circuitvalley/mipi_csi_receiver_FPGA/Cypress FX3 USB3.0 Firmware/cyfxuvcdscr.c

/*
 ## Cypress FX3 Camera Kit Source file (cyfxuvcdscr.c)
 ## ===========================
 ##
 ##  Copyright Cypress Semiconductor Corporation, 2010-2012,
 ##  All Rights Reserved
 ##  UNPUBLISHED, LICENSED SOFTWARE.
 ##
 ##  CONFIDENTIAL AND PROPRIETARY INFORMATION
 ##  WHICH IS THE PROPERTY OF CYPRESS.
 ##
 ##  Use of this file is governed
 ##  by the license agreement included in the file
 ##
 ##     <install>/license/license.txt
 ##
 ##  where <install> is the Cypress software
 ##  installation root directory path.
 ##
 ## ===========================
*/

/*
 * This file contains the USB descriptors for the FX3 HD 720p camera kit
 * application.
 */

#include "uvc.h"
#include "camera_ptzcontrol.h"
#include "uvc_settings.h"


/* Standard Device Descriptor */
const uint8_t CyFxUSBDeviceDscr[] =
    {
        0x12,                           /* Descriptor Size */
        CY_U3P_USB_DEVICE_DESCR,        /* Device Descriptor Type */
        0x10,0x02,                      /* USB 2.0 */
        0xEF,                           /* Device Class */
        0x02,                           /* Device Sub-class */
        0x01,                           /* Device protocol */
        0x40,                           /* Maxpacket size for EP0 : 64 bytes */
        0xB4,0x04,                      /* Vendor ID */
        0xF8,0x00,                      /* Product ID */
        0x00,0x00,                      /* Device release number */
        0x01,                           /* Manufacture string index */
        0x02,                           /* Product string index */
        0x00,                           /* Serial number string index */
        0x01                            /* Number of configurations */
    };

/* Device Descriptor for SS */
const uint8_t CyFxUSBDeviceDscrSS[] =
    {
        0x12,                           /* Descriptor Size */
        CY_U3P_USB_DEVICE_DESCR,        /* Device Descriptor Type */
        0x10,0x03,                      /* USB 3.10 */
        0xEF,                           /* Device Class */
        0x02,                           /* Device Sub-class */
        0x01,                           /* Device protocol */
        0x09,                           /* Maxpacket size for EP0 : 2^9 Bytes */
        0xB4,0x04,                      /* Vendor ID */
        0xF9,0x00,                      /* Product ID */
        0x00,0x00,                      /* Device release number */
        0x01,                           /* Manufacture string index */
        0x02,                           /* Product string index */
        0x00,                           /* Serial number string index */
        0x01                            /* Number of configurations */
    };

/* Standard Device Qualifier Descriptor */
const uint8_t CyFxUSBDeviceQualDscr[] =
    {
        0x0A,                           /* Descriptor Size */
        CY_U3P_USB_DEVQUAL_DESCR,       /* Device Qualifier Descriptor Type */
        0x00,0x02,                      /* USB 2.0 */
        0xEF,                           /* Device Class */
        0x02,                           /* Device Sub-class */
        0x01,                           /* Device protocol */
        0x40,                           /* Maxpacket size for EP0 : 64 bytes */
        0x01,                           /* Number of configurations */
        0x00                            /* Reserved */
    };

/* Standard Full Speed Configuration Descriptor */
const uint8_t CyFxUSBFSConfigDscr[] =
    {
        /* Configuration Descriptor Type */
        0x09,                           /* Descriptor Size */
        CY_U3P_USB_CONFIG_DESCR,        /* Configuration Descriptor Type */
        0x95,0x00,                      /* Length of this descriptor and all sub descriptors */
        0x02,                           /* Number of interfaces */
        0x01,                           /* Configuration number */
        0x00,                           /* COnfiguration string index */
        0x80,                           /* Config characteristics - Bus powered */
        0x32,                           /* Max power consumption of device (in 2mA unit) : 100mA */

        /* Interface Association Descriptor */
        0x08,                           /* Descriptor Size */
        CY_FX_INTF_ASSN_DSCR_TYPE,      /* Interface Association Descr Type: 11 */
        0x00,                           /* I/f number of first VideoControl i/f */
        0x02,                           /* Number of Video i/f */
        0x0E,                           /* CC_VIDEO : Video i/f class code */
        0x03,                           /* SC_VIDEO_INTERFACE_COLLECTION : Subclass code */
        0x00,                           /* Protocol : Not used */
        0x02,                           /* String desc index for interface */

        /* Standard Video Control Interface Descriptor */
        0x09,                           /* Descriptor size */
        CY_U3P_USB_INTRFC_DESCR,        /* Interface Descriptor type */
        0x00,                           /* Interface number */
        0x00,                           /* Alternate setting number */
        0x01,                           /* Number of end points */
        0x0E,                           /* CC_VIDEO : Interface class */
        0x01,                           /* CC_VIDEOCONTROL : Interface sub class */
        0x00,                           /* Interface protocol code */
        0x02,                           /* Interface descriptor string index */

        /* Class specific VC Interface Header Descriptor */
        0x0D,                           /* Descriptor size */
        0x24,                           /* Class Specific I/f Header Descriptor type */
        0x01,                           /* Descriptor Sub type : VC_HEADER */
        0x10, 0x01,                     /* Revision of UVC class spec: 1.1 - Minimum version required
                                           for USB Compliance. Not supported on Windows XP*/
        0x51, 0x00,                     /* Total Size of class specific descriptors (till Output terminal) */
        0x00,0x6C,0xDC,0x02,            /* Clock frequency : 48MHz(Deprecated) */
        0x01,                           /* Number of streaming interfaces */
        0x01,                           /* Video streaming I/f 1 belongs to VC i/f */

        /* Input (Camera) Terminal Descriptor */
        0x12,                           /* Descriptor size */
        0x24,                           /* Class specific interface desc type */
        0x02,                           /* Input Terminal Descriptor type */
        0x01,                           /* ID of this terminal */
        0x01,0x02,                      /* Camera terminal type */
        0x00,                           /* No association terminal */
        0x00,                           /* String desc index : Not used */
#ifdef UVC_PTZ_SUPPORT
        (uint8_t)(wObjectiveFocalLengthMin&0xFF),
        (uint8_t)((wObjectiveFocalLengthMin>>8)&0xFF),
        (uint8_t)(wObjectiveFocalLengthMax&0xFF),
        (uint8_t)((wObjectiveFocalLengthMax>>8)&0xFF),
        (uint8_t)(wOcularFocalLength&0xFF),
        (uint8_t)((wOcularFocalLength>>8)&0xFF),
#else
        0x00,0x00,                      /* No optical zoom supported */
        0x00,0x00,                      /* No optical zoom supported */
        0x00,0x00,                      /* No optical zoom supported */
#endif
        0x03,                           /* Size of controls field for this terminal : 3 bytes */
        0x00,0x00,0x00,                 /* bmControls field of camera terminal: No controls supported */

        /* Processing Unit Descriptor */
        0x0D,                           /* Descriptor size */
        0x24,                           /* Class specific interface desc type */
        0x05,                           /* Processing Unit Descriptor type */
        0x02,                           /* ID of this terminal */
        0x01,                           /* Source ID : 1 : Conencted to input terminal */
        0x00,0x40,                      /* Digital multiplier */
        0x03,                           /* Size of controls field for this terminal : 3 bytes */
        0x00,0x00,0x00,                 /* bmControls field of processing unit: Brightness control supported */
        0x00,                           /* String desc index : Not used */
        0x00,                           /* Analog Video Standards Supported: None */

        /* Extension Unit Descriptor */
        0x1C,                           /* Descriptor size */
        0x24,                           /* Class specific interface desc type */
        0x06,                           /* Extension Unit Descriptor type */
        0x03,                           /* ID of this terminal */
        0xFF,0xFF,0xFF,0xFF,            /* 16 byte GUID */
        0xFF,0xFF,0xFF,0xFF,
        0xFF,0xFF,0xFF,0xFF,
        0xFF,0xFF,0xFF,0xFF,
        0x00,                           /* Number of controls in this terminal */
        0x01,                           /* Number of input pins in this terminal */
        0x02,                           /* Source ID : 2 : Connected to Proc Unit */
        0x03,                           /* Size of controls field for this terminal : 3 bytes */
        0x00,0x00,0x00,                 /* No controls supported */
        0x00,                           /* String desc index : Not used */

        /* Output Terminal Descriptor */
        0x09,                           /* Descriptor size */
        0x24,                           /* Class specific interface desc type */
        0x03,                           /* Output Terminal Descriptor type */
        0x04,                           /* ID of this terminal */
        0x01,0x01,                      /* USB Streaming terminal type */
        0x00,                           /* No association terminal */
        0x03,                           /* Source ID : 3 : Connected to Extn Unit */
        0x00,                           /* String desc index : Not used */

        /* Video Control Status Interrupt Endpoint Descriptor */
        0x07,                           /* Descriptor size */
        CY_U3P_USB_ENDPNT_DESCR,        /* Endpoint Descriptor Type */
        CY_FX_EP_CONTROL_STATUS,        /* Endpoint address and description */
        CY_U3P_USB_EP_INTR,             /* Interrupt End point Type */
        0x40,0x00,                      /* Max packet size = 64 bytes */
        0x08,                           /* Servicing interval : 8ms */

        /* Class Specific Interrupt Endpoint Descriptor */
        0x05,                           /* Descriptor size */
        0x25,                           /* Class Specific Endpoint Descriptor Type */
        CY_U3P_USB_EP_INTR,             /* End point Sub Type */
        0x40,0x00,                      /* Max packet size = 64 bytes */

        /* Standard Video Streaming Interface Descriptor (Alternate Setting 0) */
        0x09,                           /* Descriptor size */
        CY_U3P_USB_INTRFC_DESCR,        /* Interface Descriptor type */
        0x01,                           /* Interface number */
        0x00,                           /* Alternate setting number */
        0x01,                           /* Number of end points : Zero Bandwidth */
        0x0E,                           /* Interface class : CC_VIDEO */
        0x02,                           /* Interface sub class : CC_VIDEOSTREAMING */
        0x00,                           /* Interface protocol code : Undefined */
        0x00,                           /* Interface descriptor string index */

       /* Class-specific Video Streaming Input Header Descriptor */
        0x0E,                           /* Descriptor size */
        0x24,                           /* Class-specific VS I/f Type */
        0x01,                           /* Descriptotor Subtype : Input Header */
        0x00,                           /* No format desciptor supported for FS device */
        0x0E,0x00,                      /* Total size of Class specific VS descr */
        CY_FX_EP_BULK_VIDEO,            /* EP address for BULK video data */
        0x00,                           /* No dynamic format change supported */
        0x04,                           /* Output terminal ID : 4 */
        0x01,                           /* Still image capture method 1 supported */
        0x00,                           /* Hardware trigger NOT supported */
        0x00,                           /* Hardware to initiate still image capture NOT supported */
        0x01,                           /* Size of controls field : 1 byte */
        0x00,                           /* D2 : Compression quality supported */

        /* Endpoint Descriptor for BULK Streaming Video Data */
        0x07,                           /* Descriptor size */
        CY_U3P_USB_ENDPNT_DESCR,        /* Endpoint Descriptor Type */
        CY_FX_EP_BULK_VIDEO,            /* Endpoint address and description */
        0x02,                           /* BULK End point */
        0x40,                           /* EP Packet Size: 64 bytes */
        0x00,
        0x00                            /* Servicing interval for data transfers */
    };

/* Standard High Speed Configuration Descriptor */
const uint8_t CyFxUSBHSConfigDscr[] =
    {
        /* Configuration Descriptor Type */
        0x09,                           /* Descriptor Size */
        CY_U3P_USB_CONFIG_DESCR,        /* Configuration Descriptor Type */
#ifdef USB_DEBUG_INTERFACE
#ifdef FX3_UVC_1_0_SUPPORT
        0xE4,0x00,                      /* Length of this descriptor and all sub descriptors */
#else
        0xE5,0x00,                      /* Length of this descriptor and all sub descriptors */
#endif
        0x03,                           /* Number of interfaces */
#else
#ifdef FX3_UVC_1_0_SUPPORT
        0xCD,0x00,                      /* Length of this descriptor and all sub descriptors */
#else
        0xCE,0x00,                      /* Length of this descriptor and all sub descriptors */
#endif
        0x02,                           /* Number of interfaces */
#endif
        0x01,                           /* Configuration number */
        0x00,                           /* COnfiguration string index */
        0x80,                           /* Config characteristics - Bus powered */
        0xFA,                           /* Max power consumption of device (in 2mA unit) : 500mA */

        /* Interface Association Descriptor */
        0x08,                           /* Descriptor Size */
        CY_FX_INTF_ASSN_DSCR_TYPE,      /* Interface Association Descr Type: 11 */
        0x00,                           /* I/f number of first VideoControl i/f */
        0x02,                           /* Number of Video i/f */
        0x0E,                           /* CC_VIDEO : Video i/f class code */
        0x03,                           /* SC_VIDEO_INTERFACE_COLLECTION : Subclass code */
        0x00,                           /* Protocol : Not used */
        0x02,                           /* String desc index for interface */

        /* Standard Video Control Interface Descriptor */
        0x09,                           /* Descriptor size */
        CY_U3P_USB_INTRFC_DESCR,        /* Interface Descriptor type */
        0x00,                           /* Interface number */
        0x00,                           /* Alternate setting number */
        0x01,                           /* Number of end points */
        0x0E,                           /* CC_VIDEO : Interface class */
        0x01,                           /* CC_VIDEOCONTROL : Interface sub class */
        0x00,                           /* Interface protocol code */
        0x02,                           /* Interface descriptor string index */

        /* Class specific VC Interface Header Descriptor */
        0x0D,                           /* Descriptor size */
        0x24,                           /* Class Specific I/f Header Descriptor type */
        0x01,                           /* Descriptor Sub type : VC_HEADER */
#ifdef FX3_UVC_1_0_SUPPORT
        0x00, 0x01,                     /* Revision of UVC class spec: 1.0 - Legacy version */
        0x50, 0x00,                     /* Total Size of class specific descriptors (till Output terminal) */
#else
        0x10, 0x01,                     /* Revision of UVC class spec: 1.1 - Minimum version required
                                           for USB Compliance. Not supported on Windows XP*/
        0x51, 0x00,                     /* Total Size of class specific descriptors (till Output terminal) */
#endif
        0x00,0x6C,0xDC,0x02,            /* Clock frequency : 48MHz(Deprecated) */
        0x01,                           /* Number of streaming interfaces */
        0x01,                           /* Video streaming I/f 1 belongs to VC i/f */

        /* Input (Camera) Terminal Descriptor */
        0x12,                           /* Descriptor size */
        0x24,                           /* Class specific interface desc type */
        0x02,                           /* Input Terminal Descriptor type */
        0x01,                           /* ID of this terminal */
        0x01,0x02,                      /* Camera terminal type */
        0x00,                           /* No association terminal */
        0x00,                           /* String desc index : Not used */
#ifdef UVC_PTZ_SUPPORT
        (uint8_t)(wObjectiveFocalLengthMin&0xFF),
        (uint8_t)((wObjectiveFocalLengthMin>>8)&0xFF),
        (uint8_t)(wObjectiveFocalLengthMax&0xFF),
        (uint8_t)((wObjectiveFocalLengthMax>>8)&0xFF),
        (uint8_t)(wOcularFocalLength&0xFF),
        (uint8_t)((wOcularFocalLength>>8)&0xFF),
#else
        0x00,0x00,                      /* No optical zoom supported */
        0x00,0x00,                      /* No optical zoom supported */
        0x00,0x00,                      /* No optical zoom supported */
#endif
        0x03,                           /* Size of controls field for this terminal : 3 bytes */
                                        /* A bit set to 1 indicates that the mentioned Control is
                                         * supported for the video stream in the bmControls field
                                         * D0: Scanning Mode
                                         * D1: Auto-Exposure Mode
                                         * D2: Auto-Exposure Priority
                                         * D3: Exposure Time (Absolute)
                                         * D4: Exposure Time (Relative)
                                         * D5: Focus (Absolute)
                                         * D6: Focus (Relative)
                                         * D7: Iris (Absolute)
                                         * D8: Iris (Relative)
                                         * D9: Zoom (Absolute)
                                         * D10: Zoom (Relative)
                                         * D11: PanTilt (Absolute)
                                         * D12: PanTilt (Relative)
                                         * D13: Roll (Absolute)
                                         * D14: Roll (Relative)
                                         * D15: Reserved
                                         * D16: Reserved
                                         * D17: Focus, Auto
                                         * D18: Privacy
                                         * D19: Focus, Simple
                                         * D20: Window
                                         * D21: Region of Interest
                                         * D22 – D23: Reserved, set to zero
                                         */
#ifdef UVC_PTZ_SUPPORT
        0x00,0x0A,0x00,                 /* bmControls field of camera terminal: PTZ supported */
#else
        0x00,0x00,0x00,                 /* bmControls field of camera terminal: No controls supported */
#endif

        /* Processing Unit Descriptor */
#ifdef FX3_UVC_1_0_SUPPORT
        0x0C,                           /* Descriptor size */
#else
        0x0D,                           /* Descriptor size */
#endif
        0x24,                           /* Class specific interface desc type */
        0x05,                           /* Processing Unit Descriptor type */
        0x02,                           /* ID of this terminal */
        0x01,                           /* Source ID : 1 : Conencted to input terminal */
        0x00,0x40,                      /* Digital multiplier */
        0x03,                           /* Size of controls field for this terminal : 3 bytes */
                                        /* A bit set to 1 in the bmControls field indicates that
                                         * the mentioned Control is supported for the video stream.
                                         * D0: Brightness
                                         * D1: Contrast
                                         * D2: Hue
                                         * D3: Saturation
                                         * D4: Sharpness
                                         * D5: Gamma
                                         * D6: White Balance Temperature
                                         * D7: White Balance Component
                                         * D8: Backlight Compensation
                                         * D9: Gain
                                         * D10: Power Line Frequency
                                         * D11: Hue, Auto
                                         * D12: White Balance Temperature, Auto
                                         * D13: White Balance Component, Auto
                                         * D14: Digital Multiplier
                                         * D15: Digital Multiplier Limit
                                         * D16: Analog Video Standard
                                         * D17: Analog Video Lock Status
                                         * D18: Contrast, Auto
                                         * D19 – D23: Reserved. Set to zero.
                                         */
        0x01,0x00,0x00,                 /* bmControls field of processing unit: Brightness control supported */
        0x00,                           /* String desc index : Not used */
#ifndef FX3_UVC_1_0_SUPPORT
        0x00,                           /* Analog Video Standards Supported: None */
#endif

#ifdef UVC_EXTENSION_UNIT
        /* Extension Unit Descriptor */
        0x1C,                           /* Descriptor size */
        0x24,                           /* Class specific interface desc type */
        0x06,                           /* Extension Unit Descriptor type */
        0x03,                           /* ID of this terminal */
        //static const GUID <<name>> =
        //{ 0xacb6890c, 0xa3b3, 0x4060,{ 0x8b, 0x9a, 0xdf, 0x34, 0xee, 0xf3, 0x9a, 0x2e } };
        0x0C, 0x89, 0xB6, 0xAC,         /* GUID specific to AN75779 firmware. Obtained from Visual studio */
        0xB3, 0xA3, 0x60, 0x40,
        0x8B, 0x9A, 0xDF, 0x34,
        0xEE, 0xF3, 0x9A, 0x2E,
        0x01,                           /* Number of controls in this terminal */
        0x01,                           /* Number of input pins in this terminal */
        0x02,                           /* Source ID : 2 : Connected to Proc Unit */
        0x03,                           /* Size of controls field for this terminal : 3 bytes */
        0x01, 0x00, 0x00,               /* Controls supported */
        0x00,                           /* String descriptor index : Not used */
#else
        /* Extension Unit Descriptor */
        0x1C,                           /* Descriptor size */
        0x24,                           /* Class specific interface desc type */
        0x06,                           /* Extension Unit Descriptor type */
        0x03,                           /* ID of this terminal */
        0xFF,0xFF,0xFF,0xFF,            /* 16 byte GUID */
        0xFF,0xFF,0xFF,0xFF,
        0xFF,0xFF,0xFF,0xFF,
        0xFF,0xFF,0xFF,0xFF,
        0x00,                           /* Number of controls in this terminal */
        0x01,                           /* Number of input pins in this terminal */
        0x02,                           /* Source ID : 2 : Connected to Proc Unit */
        0x03,                           /* Size of controls field for this terminal : 3 bytes */
        0x00,0x00,0x00,                 /* No controls supported */
        0x00,                           /* String desc index : Not used */
#endif

        /* Output Terminal Descriptor */
        0x09,                           /* Descriptor size */
        0x24,                           /* Class specific interface desc type */
        0x03,                           /* Output Terminal Descriptor type */
        0x04,                           /* ID of this terminal */
        0x01,0x01,                      /* USB Streaming terminal type */
        0x00,                           /* No association terminal */
        0x03,                           /* Source ID : 3 : Connected to Extn Unit */
        0x00,                           /* String desc index : Not used */

        /* Video Control Status Interrupt Endpoint Descriptor */
        0x07,                           /* Descriptor size */
        CY_U3P_USB_ENDPNT_DESCR,        /* Endpoint Descriptor Type */
        CY_FX_EP_CONTROL_STATUS,        /* Endpoint address and description */
        CY_U3P_USB_EP_INTR,             /* Interrupt End point Type */
        0x40,0x00,                      /* Max packet size = 64 bytes */
        0x08,                           /* Servicing interval : 8ms */

        /* Class Specific Interrupt Endpoint Descriptor */
        0x05,                           /* Descriptor size */
        0x25,                           /* Class Specific Endpoint Descriptor Type */
        CY_U3P_USB_EP_INTR,             /* End point Sub Type */
        0x40,0x00,                      /* Max packet size = 64 bytes */

        /* Standard Video Streaming Interface Descriptor (Alternate Setting 0) */
        0x09,                           /* Descriptor size */
        CY_U3P_USB_INTRFC_DESCR,        /* Interface Descriptor type */
        0x01,                           /* Interface number */
        0x00,                           /* Alternate setting number */
        0x01,                           /* Number of end points : Zero Bandwidth */
        0x0E,                           /* Interface class : CC_VIDEO */
        0x02,                           /* Interface sub class : CC_VIDEOSTREAMING */
        0x00,                           /* Interface protocol code : Undefined */
        0x00,                           /* Interface descriptor string index */

       /* Class-specific Video Streaming Input Header Descriptor */
        0x0E,                           /* Descriptor size */
        0x24,                           /* Class-specific VS I/f Type */
        0x01,                           /* Descriptotor Subtype : Input Header */
        0x01,                           /* 1 format desciptor follows */
        0x47,0x00,                      /* Total size of Class specific VS descr */
        CY_FX_EP_BULK_VIDEO,            /* EP address for BULK video data */
        0x00,                           /* No dynamic format change supported */
        0x04,                           /* Output terminal ID : 4 */
        0x01,                           /* Still image capture method 1 supported */
        0x00,                           /* Hardware trigger NOT supported */
        0x00,                           /* Hardware to initiate still image capture NOT supported */
        0x01,                           /* Size of controls field : 1 byte */
        0x00,                           /* D2 : Compression quality supported */

       /* Class specific Uncompressed VS format descriptor */
        0x1B,                           /* Descriptor size */
        0x24,                           /* Class-specific VS I/f Type */
        0x04,                           /* Subtype : uncompressed format I/F */
        0x01,                           /* Format desciptor index (only one format is supported) */
        0x01,                           /* number of frame descriptor followed */
        0x59,0x55,0x59,0x32,            /* GUID used to identify streaming-encoding format: YUY2  */
        0x00,0x00,0x10,0x00,
        0x80,0x00,0x00,0xAA,
        0x00,0x38,0x9B,0x71,
        0x10,                           /* Number of bits per pixel used to specify color in the decoded video frame.
                                           0 if not applicable: 16 bit per pixel */
        0x01,                           /* Optimum Frame Index for this stream: 1 */
        0x08,                           /* X dimension of the picture aspect ratio: Non-interlaced in progressive scan */
        0x06,                           /* Y dimension of the picture aspect ratio: Non-interlaced in progressive scan*/
        0x00,                           /* Interlace Flags: Progressive scanning, no interlace */
        0x00,                           /* duplication of the video stream restriction: 0 - no restriction */

       /* Class specific Uncompressed VS Frame descriptor */
        0x1E,                           /* Descriptor size */
        0x24,                           /* Descriptor type*/
        0x05,                           /* Subtype: uncompressed frame I/F */
        FRAME_640x480,                           /* Frame Descriptor Index */
        0x00,                           /* Still image capture method 1 supported */
        WBVAL(UVC_WIDTH_640),                  /* Width in pixel: 640*/
        WBVAL(UVC_HEIGHT_480),                 /* Height in pixel 480*/
        DBVAL(MIN_BIT_RATE_640x480),           /* Min bit rate bits/s. */
        DBVAL(MAX_BIT_RATE_640x480),           /* Max bit rate bits/s. */
        DBVAL(MAX_FRAME_SIZE_640x480),         /* Maximum video or still frame size in bytes(Deprecated) */
        DBVAL(INTERVAL_30),            /* Default Frame Interval */
        0x01,                           /* Frame interval(Frame Rate) types: Only one frame interval supported */
        DBVAL(INTERVAL_30),            /* Shortest Frame Interval */

        /* Endpoint Descriptor for BULK Streaming Video Data */
        0x07,                           /* Descriptor size */
        CY_U3P_USB_ENDPNT_DESCR,        /* Endpoint Descriptor Type */
        CY_FX_EP_BULK_VIDEO,            /* Endpoint address and description */
        0x02,                           /* BULK End point */
        (uint8_t)(512 & 0x00FF),        /* High speed max packet size is always 512 bytes. */
        (uint8_t)((512 & 0xFF00)>>8),
        0x00                            /* Servicing interval for data transfers */

#ifdef USB_DEBUG_INTERFACE
        ,
        0x09,                           /* Descriptor size */
        CY_U3P_USB_INTRFC_DESCR,        /* Interface Descriptor type */
        0x02,                           /* Interface number */
        0x00,                           /* Alternate setting number */
        0x02,                           /* Number of end points */
        0xFF,                           /* Interface class */
        0x00,                           /* Interface sub class */
        0x00,                           /* Interface protocol code */
        0x00,                           /* Interface descriptor string index */

        /* Endpoint descriptor for producer EP */
        0x07,                           /* Descriptor size */
        CY_U3P_USB_ENDPNT_DESCR,        /* Endpoint descriptor type */
        CY_FX_EP_DEBUG_CMD,             /* Endpoint address and description */
        CY_U3P_USB_EP_BULK,             /* Bulk endpoint type */
        0x00,0x02,                      /* Max packet size = 512 bytes */
        0x00,                           /* Servicing interval for data transfers : 0 for bulk */
    
        /* Endpoint descriptor for consumer EP */
        0x07,                           /* Descriptor size */
        CY_U3P_USB_ENDPNT_DESCR,        /* Endpoint descriptor type */
        CY_FX_EP_DEBUG_RSP,             /* Endpoint address and description */
        CY_U3P_USB_EP_BULK,             /* Bulk endpoint type */
        0x00,0x02,                      /* Max packet size = 512 bytes */
        0x00                            /* Servicing interval for data transfers : 0 for Bulk */
#endif
    };

/* BOS for SS */

#define CY_FX_BOS_DSCR_TYPE             15
#define CY_FX_DEVICE_CAPB_DSCR_TYPE     16
#define CY_FX_SS_EP_COMPN_DSCR_TYPE     48

/* Device Capability Type Codes */
#define CY_FX_WIRELESS_USB_CAPB_TYPE    1
#define CY_FX_USB2_EXTN_CAPB_TYPE       2
#define CY_FX_SS_USB_CAPB_TYPE          3
#define CY_FX_CONTAINER_ID_CAPBD_TYPE   4

const uint8_t CyFxUSBBOSDscr[] =
{
        0x05,                           /* Descriptor Size */
        CY_FX_BOS_DSCR_TYPE,            /* Device Descriptor Type */
        0x16,0x00,                      /* Length of this descriptor and all sub descriptors */
        0x02,                           /* Number of device capability descriptors */

        /* USB 2.0 Extension */
        0x07,                           /* Descriptor Size */
        CY_FX_DEVICE_CAPB_DSCR_TYPE,    /* Device Capability Type descriptor */
        CY_FX_USB2_EXTN_CAPB_TYPE,      /* USB 2.0 Extension Capability Type */
        0x1E,0x64,0x00,0x00,            /* Supported device level features: LPM support, BESL supported,
                                           Baseline BESL=400 us, Deep BESL=1000 us. */

        /* SuperSpeed Device Capability */
        0x0A,                           /* Descriptor Size */
        CY_FX_DEVICE_CAPB_DSCR_TYPE,    /* Device Capability Type descriptor */
        CY_FX_SS_USB_CAPB_TYPE,         /* SuperSpeed Device Capability Type */
        0x00,                           /* Supported device level features  */
        0x0E,0x00,                      /* Speeds Supported by the device : SS, HS and FS */
        0x03,                           /* Functionality support */
        0x00,                           /* U1 Device Exit Latency */
        0x00,0x00                       /* U2 Device Exit Latency */
};

/* Super Speed Configuration Descriptor */
const uint8_t CyFxUSBSSConfigDscr[] =
    {

        /* Configuration Descriptor Type */
        0x09,                           /* Descriptor Size */
        CY_U3P_USB_CONFIG_DESCR,        /* Configuration Descriptor Type */
#ifdef USB_DEBUG_INTERFACE
	#ifdef FX3_UVC_1_0_SUPPORT
			0xFC,0x00,                      /* Total length of this and all sub-descriptors. */
	#else
			0xFD,0x00,                      /* Total length of this and all sub-descriptors. */
	#endif
			0x03,                           /* Number of interfaces */
#else
	#ifdef FX3_UVC_1_0_SUPPORT
			0xD9,0x00,                      /* Length of this descriptor and all sub descriptors */
	#else
			0x80,0x01,                      /* Length of this descriptor and all sub descriptors */
	#endif
        0x02,                           /* Number of interfaces */
#endif
        0x01,                           /* Configuration number */
        0x00,                           /* Configuration string index */
        0x80,                           /* Config characteristics - Bus powered */
        0x32,                           /* Max power consumption of device (in 8mA unit) : 400mA */

        /* Interface Association Descriptor */
        0x08,                           /* Descriptor Size */
        CY_FX_INTF_ASSN_DSCR_TYPE,      /* Interface Association Descr Type: 11 */
        0x00,                           /* I/f number of first VideoControl i/f */
        0x02,                           /* Number of Video i/f */
        0x0E,                           /* CC_VIDEO : Video i/f class code */
        0x03,                           /* SC_VIDEO_INTERFACE_COLLECTION : Subclass code */
        0x00,                           /* Protocol : Not used */
        0x02,                           /* String desc index for interface */

        /* Standard Video Control Interface Descriptor */
        0x09,                           /* Descriptor size */
        CY_U3P_USB_INTRFC_DESCR,        /* Interface Descriptor type */
        0x00,                           /* Interface number */
        0x00,                           /* Alternate setting number */
        0x01,                           /* Number of end points */
        0x0E,                           /* CC_VIDEO : Interface class */
        0x01,                           /* CC_VIDEOCONTROL : Interface sub class */
        0x00,                           /* Interface protocol code */
        0x02,                           /* Interface descriptor string index */

        /* Class specific VC Interface Header Descriptor */
        0x0D,                           /* Descriptor size */
        0x24,                           /* Class Specific I/f Header Descriptor type */
        0x01,                           /* Descriptor Sub type : VC_HEADER */
#ifdef FX3_UVC_1_0_SUPPORT
        0x00, 0x01,                     /* Revision of UVC class spec: 1.0 - Legacy version */
        0x50, 0x00,                     /* Total Size of class specific descriptors (till Output terminal) */
#else
        0x10, 0x01,                     /* Revision of UVC class spec: 1.1 - Minimum version required
                                           for USB Compliance. Not supported on Windows XP*/
        0x51, 0x00,                     /* Total Size of class specific descriptors (till Output terminal) */
#endif
        0x00,0x6C,0xDC,0x02,            /* Clock frequency : 48MHz(Deprecated) */
        0x01,                           /* Number of streaming interfaces */
        0x01,                           /* Video streaming I/f 1 belongs to VC i/f */

        /* Input (Camera) Terminal Descriptor */
        0x12,                           /* Descriptor size */
        0x24,                           /* Class specific interface desc type */
        0x02,                           /* Input Terminal Descriptor type */
        0x01,                           /* ID of this terminal */
        0x01,0x02,                      /* Camera terminal type */
        0x00,                           /* No association terminal */
        0x00,                           /* String desc index : Not used */
#ifdef UVC_PTZ_SUPPORT
        (uint8_t)(wObjectiveFocalLengthMin&0xFF),
        (uint8_t)((wObjectiveFocalLengthMin>>8)&0xFF),
        (uint8_t)(wObjectiveFocalLengthMax&0xFF),
        (uint8_t)((wObjectiveFocalLengthMax>>8)&0xFF),
        (uint8_t)(wOcularFocalLength&0xFF),
        (uint8_t)((wOcularFocalLength>>8)&0xFF),
#else
        0x00,0x00,                      /* No optical zoom supported */
        0x00,0x00,                      /* No optical zoom supported */
        0x00,0x00,                      /* No optical zoom supported */
#endif
        0x03,                           /* Size of controls field for this terminal : 3 bytes */
                                        /* A bit set to 1 in the bmControls field indicates that
                                         * the mentioned Control is supported for the video stream.
                                         * D0: Scanning Mode
                                         * D1: Auto-Exposure Mode
                                         * D2: Auto-Exposure Priority
                                         * D3: Exposure Time (Absolute)
                                         * D4: Exposure Time (Relative)
                                         * D5: Focus (Absolute)
                                         * D6: Focus (Relative)
                                         * D7: Iris (Absolute)
                                         * D8: Iris (Relative)
                                         * D9: Zoom (Absolute)
                                         * D10: Zoom (Relative)
                                         * D11: PanTilt (Absolute)
                                         * D12: PanTilt (Relative)
                                         * D13: Roll (Absolute)
                                         * D14: Roll (Relative)
                                         * D15: Reserved
                                         * D16: Reserved
                                         * D17: Focus, Auto
                                         * D18: Privacy
                                         * D19: Focus, Simple
                                         * D20: Window
                                         * D21: Region of Interest
                                         * D22 – D23: Reserved, set to zero
                                         */
#ifdef UVC_PTZ_SUPPORT
        0x08,0x00,0x00,                 /* bmControls field of camera terminal: PTZ supported only Exposure */
#else
        0x00,0x00,0x00,                 /* bmControls field of camera terminal: No controls supported */
#endif

        /* Processing Unit Descriptor */
#ifdef FX3_UVC_1_0_SUPPORT
        0x0C,                           /* Descriptor size */
#else
        0x0D,                           /* Descriptor size */
#endif
        0x24,                           /* Class specific interface desc type */
        0x05,                           /* Processing Unit Descriptor type */
        0x02,                           /* ID of this terminal */
        0x01,                           /* Source ID : 1 : Connected to input terminal */
        0x00,0x40,                      /* Digital multiplier */
        0x03,                           /* Size of controls field for this terminal : 3 bytes */
        0x29,0x00,0x00,                 /* bmControls field of processing unit: Brightness, Gamma is used as test pattern*/
        0x00,                           /* String desc index : Not used */
#ifndef FX3_UVC_1_0_SUPPORT
        0x00,                           /* Analog Video Standards Supported: None */
#endif

#ifdef UVC_EXTENSION_UNIT
        /* Extension Unit Descriptor */
        0x1C,                           /* Descriptor size */
        0x24,                           /* Class specific interface desc type */
        0x06,                           /* Extension Unit Descriptor type */
        0x03,                           /* ID of this terminal */
        //static const GUID <<name>> =
        //{ 0xacb6890c, 0xa3b3, 0x4060,{ 0x8b, 0x9a, 0xdf, 0x34, 0xee, 0xf3, 0x9a, 0x2e } };
        0x0C, 0x89, 0xB6, 0xAC,         /* GUID specific to AN75779 firmware. Obtained from Visual studio */
        0xB3, 0xA3, 0x60, 0x40,
        0x8B, 0x9A, 0xDF, 0x34,
        0xEE, 0xF3, 0x9A, 0x2E,
        0x01,                           /* Number of controls in this terminal */
        0x01,                           /* Number of input pins in this terminal */
        0x02,                           /* Source ID : 2 : Connected to Proc Unit */
        0x03,                           /* Size of controls field for this terminal : 3 bytes */
        0x01, 0x00, 0x00,               /* Controls supported */
        0x00,                           /* String descriptor index : Not used */
#else
        /* Extension Unit Descriptor */
        0x1C,                           /* Descriptor size */
        0x24,                           /* Class specific interface desc type */
        0x06,                           /* Extension Unit Descriptor type */
        0x03,                           /* ID of this terminal */
        0xFF,0xFF,0xFF,0xFF,            /* 16 byte GUID */
        0xFF,0xFF,0xFF,0xFF,
        0xFF,0xFF,0xFF,0xFF,
        0xFF,0xFF,0xFF,0xFF,
        0x00,                           /* Number of controls in this terminal */
        0x01,                           /* Number of input pins in this terminal */
        0x02,                           /* Source ID : 2 : Connected to Proc Unit */
        0x03,                           /* Size of controls field for this terminal : 3 bytes */
        0x00,0x00,0x00,                 /* No controls supported */
        0x00,                           /* String desc index : Not used */
#endif

        /* Output Terminal Descriptor */
        0x09,                           /* Descriptor size */
        0x24,                           /* Class specific interface desc type */
        0x03,                           /* Output Terminal Descriptor type */
        0x04,                           /* ID of this terminal */
        0x01,0x01,                      /* USB Streaming terminal type */
        0x00,                           /* No association terminal */
        0x03,                           /* Source ID : 3 : Connected to Extn Unit */
        0x00,                           /* String desc index : Not used */

        /* Video Control Status Interrupt Endpoint Descriptor */
        0x07,                           /* Descriptor size */
        CY_U3P_USB_ENDPNT_DESCR,        /* Endpoint Descriptor Type */
        CY_FX_EP_CONTROL_STATUS,        /* Endpoint address and description */
        CY_U3P_USB_EP_INTR,             /* Interrupt End point Type */
        0x40,0x00,                      /* Max packet size = 64 bytes */
        0x01,                           /* Servicing interval */

        /* Super Speed Endpoint Companion Descriptor */
        0x06,                           /* Descriptor size */
        CY_U3P_SS_EP_COMPN_DESCR,       /* SS Endpoint Companion Descriptor Type */
        0x00,                           /* Max no. of packets in a Burst : 1 */
        0x00,                           /* Attribute: N.A. */
        0x00,                           /* Bytes per interval:1024 */
        0x04,

        /* Class Specific Interrupt Endpoint Descriptor */
        0x05,                           /* Descriptor size */
        0x25,                           /* Class Specific Endpoint Descriptor Type */
        CY_U3P_USB_EP_INTR,             /* End point Sub Type */
        0x40,0x00,                      /* Max packet size = 64 bytes */


        /* Standard Video Streaming Interface Descriptor (Alternate Setting 0) */
        0x09,                           /* Descriptor size */
        CY_U3P_USB_INTRFC_DESCR,        /* Interface Descriptor type */
        0x01,                           /* Interface number */
        0x00,                           /* Alternate setting number */
        0x01,                           /* Number of end points */
        0x0E,                           /* Interface class : CC_VIDEO */
        0x02,                           /* Interface sub class : CC_VIDEOSTREAMING */
        0x00,                           /* Interface protocol code : Undefined */
        0x00,                           /* Interface descriptor string index */

       /* Class-specific Video Streaming Input Header Descriptor */
        0x0E,                           /* Descriptor size */
        0x24,                           /* Class-specific VS I/f Type */
        0x01,                           /* Descriptotor Subtype : Input Header */
        0x01,                           /* 1 format desciptor follows */
        0xED,0x00,                      /* Total size of Class specific VS descr */
        CY_FX_EP_BULK_VIDEO,            /* EP address for BULK video data */
        0x00,                           /* No dynamic format change supported , Hardware button on Camera?*/
        0x04,                           /* Output terminal ID : 4 */
        0x01,                           /* Still image capture method 1 supported */
        0x00,                           /* Hardware trigger NOT supported */
        0x00,                           /* Hardware to initiate still image capture NOT supported */
        0x01,                           /* Size of controls field : 1 byte */
        0x00,                           /* D2 : Compression quality supported */

        /* Class specific Uncompressed VS format descriptor */
        0x1B,                           /* Descriptor size */
        0x24,                           /* Class-specific VS I/f Type */
        0x04,                           /* Subtype : uncompressed format I/F */
        0x01,                           /* Format desciptor index */
        0x06,                           /* Number of frame descriptor followed */
        0x59,0x55,0x59,0x32,            /* GUID used to identify streaming-encoding format: YUY2  */
        0x00,0x00,0x10,0x00,
        0x80,0x00,0x00,0xAA,
        0x00,0x38,0x9B,0x71,
        0x10,                           /* Number of bits per pixel */
        0x01,                           /* Optimum Frame Index for this stream: 1 */
        0x10,                           /* X dimension of the picture aspect ratio; Non-interlaced */
        0x09,                           /* Y dimension of the pictuer aspect ratio: Non-interlaced */
        0x00,                           /* Interlace Flags: Progressive scanning, no interlace */
        0x00,                           /* duplication of the video stream restriction: 0 - no restriction */

        /* Class specific Uncompressed VS frame descriptor */
        0x22,                           /* Descriptor size */
        0x24,                           /* Descriptor type*/
        0x05,                           /* Subtype: uncompressed frame I/F */
        FRAME_640x480,                  /* Frame Descriptor Index */
        0x00,                           /* Still image capture method 1 supported */
        WBVAL(UVC_WIDTH_640),                  /* Width in pixel: 640*/
        WBVAL(UVC_HEIGHT_480),                 /* Height in pixel 480*/
        DBVAL(MIN_BIT_RATE_640x480),           /* Min bit rate bits/s. */
        DBVAL(MAX_BIT_RATE_640x480),           /* Max bit rate bits/s. */
        DBVAL(MAX_FRAME_SIZE_640x480),         /* Maximum video or still frame size in bytes(Deprecated) */
        DBVAL(INTERVAL_30),            /* Default Frame Interval */
        0x02,                          /* Frame interval(Frame Rate) types: Only two frame interval supported for this resolution*/
        DBVAL(INTERVAL_200),           /* Frame Interval 200 */
        DBVAL(INTERVAL_30),            /* Frame Interval 30 */

        0x26,                           /* Descriptor size */
        0x24,                           /* Descriptor type*/
        0x05,                           /* Subtype: uncompressed frame I/F */
        FRAME_1280x720,                           /* Frame Descriptor Index */
        0x00,                           /* Still image capture method 1 supported */
        WBVAL(UVC_WIDTH_1280),                      /* Width in pixel: 1280 */
        WBVAL(UVC_HEIGHT_720),                      /* Height in pixel 720 HD */
        DBVAL(MIN_BIT_RATE_1280x720),            /* Min bit rate bits/s. */
        DBVAL(MAX_BIT_RATE_1280x720),            /* Max bit rate bits/s. */
        DBVAL(MAX_FRAME_SIZE_1280x720),            /* Maximum video or still frame size in bytes(Deprecated) */
        DBVAL(INTERVAL_30),            /* Default Frame Interval */
        0x03,                           /* Frame interval(Frame Rate) types: Three frame interval supported for this resolution*/
        DBVAL(INTERVAL_120),            /*  Frame Interval 120 FPS */
        DBVAL(INTERVAL_60),            /*  Frame Interval 60 FPS */
        DBVAL(INTERVAL_30),            /*  Frame Interval 30 FPS*/

        0x22,                           /* Descriptor size */
        0x24,                           /* Descriptor type*/
        0x05,                           /* Subtype: uncompressed frame I/F */
        FRAME_1920x1080,                           /* Frame Descriptor Index */
        0x00,                           /* Still image capture method 1 supported */
        WBVAL(UVC_WIDTH_1920),                      /* Width in pixel: 1920 */
        WBVAL(UVC_HEIGHT_1080),                      /* Height in pixel 1080 HD */
        DBVAL(MIN_BIT_RATE_1920x1080),            /* Min bit rate bits/s. */
        DBVAL(MAX_BIT_RATE_1920x1080),            /* Max bit rate bits/s. */
        DBVAL(MAX_FRAME_SIZE_1920x1080),            /* Maximum video or still frame size in bytes(Deprecated) */
        DBVAL(INTERVAL_30),            /* Default Frame Interval */
        0x02,                           /* Frame interval(Frame Rate) types: Only two frame interval supported for this resolution*/
        DBVAL(INTERVAL_60),            /* Frame Interval 60FPS*/
        DBVAL(INTERVAL_30),            /* Frame Interval 30FPS*/

        0x1E,                           /* Descriptor size */
        0x24,                           /* Descriptor type*/
        0x05,                           /* Subtype: uncompressed frame I/F */
        FRAME_3280x2462,                           /* Frame Descriptor Index */
        0x00,                           /* Still image capture method 1 supported */
        WBVAL(UVC_WIDTH_3280),                      /* Width in pixel: 3280 */
        WBVAL(UVC_HEIGHT_2462),                      /* Height in pixel 2464 HD */
        DBVAL(MIN_BIT_RATE_3280x2462),            /* Min bit rate bits/s. */
        DBVAL(MAX_BIT_RATE_3280x2462),            /* Max bit rate bits/s. */
        DBVAL(MAX_FRAME_SIZE_3280x2462),            /* Maximum video or still frame size in bytes(Deprecated) */
        DBVAL(INTERVAL_15),            /* Default Frame Interval */
        0x01,                           /* Frame interval(Frame Rate) types: Only one frame interval supported for this resolution*/
        DBVAL(INTERVAL_15),            /* Shortest Frame Interval */

        0x1E,                           /* Descriptor size */
        0x24,                           /* Descriptor type*/
        0x05,                           /* Subtype: uncompressed frame I/F */
        FRMAE_640x128,                           /* Frame Descriptor Index */
        0x00,                           /* Still image capture method 1 supported */
        WBVAL(UVC_WIDTH_640),                      /* Width in pixel: 640 */
        WBVAL(UVC_HEIGHT_126),                      /* Height in pixel 126 */
        DBVAL(MIN_BIT_RATE_640x126),            /* Min bit rate bits/s. */
        DBVAL(MAX_BIT_RATE_640x126),            /* Max bit rate bits/s. */
        DBVAL(MAX_FRAME_SIZE_640x126),            /* Maximum video or still frame size in bytes(Deprecated) */
        DBVAL(INTERVAL_682),            /* Default Frame Interval */
        0x01,                           /* Frame interval(Frame Rate) types: Only one frame interval supported for this resolution*/
        DBVAL(INTERVAL_682),            /* Shortest Frame Interval */

        0x1E,                           /* Descriptor size */
        0x24,                           /* Descriptor type*/
        0x05,                           /* Subtype: uncompressed frame I/F */
        FRMAE_640x80,                           /* Frame Descriptor Index */
        0x00,                           /* Still image capture method 1 supported */
        WBVAL(UVC_WIDTH_640),                      /* Width in pixel: 640 */
        WBVAL(UVC_HEIGHT_78),                      /* Height in pixel 126 */
        DBVAL(MIN_BIT_RATE_640x78),            /* Min bit rate bits/s. */
        DBVAL(MAX_BIT_RATE_640x78),            /* Max bit rate bits/s. */
        DBVAL(MAX_FRAME_SIZE_640x78),            /* Maximum video or still frame size in bytes(Deprecated) */
        DBVAL(INTERVAL_1000),            /* Default Frame Interval */
        0x01,                           /* Frame interval(Frame Rate) types: Only one frame interval supported for this resolution*/
        DBVAL(INTERVAL_1000),            /* Shortest Frame Interval */

        /* Endpoint Descriptor for BULK Streaming Video Data */
        0x07,                           /* Descriptor size */
        CY_U3P_USB_ENDPNT_DESCR,        /* Endpoint Descriptor Type */
        CY_FX_EP_BULK_VIDEO,            /* Endpoint address and description */
        CY_U3P_USB_EP_BULK,             /* BULK End point */
        CY_FX_EP_BULK_VIDEO_PKT_SIZE_L, /* EP MaxPcktSize: 1024B */
        CY_FX_EP_BULK_VIDEO_PKT_SIZE_H, /* EP MaxPcktSize: 1024B */
        0x00,                           /* Servicing interval for data transfers */

        /* Super Speed Endpoint Companion Descriptor */
        0x06,                           /* Descriptor size */
        CY_U3P_SS_EP_COMPN_DESCR,       /* SS Endpoint Companion Descriptor Type */
        0x0F,                           /* Max number of packets per burst: 16 */
        0x00,                           /* Attribute: Streams not defined */
        0x00,                           /* No meaning for bulk */
        0x00

#ifdef USB_DEBUG_INTERFACE
        ,
        0x09,                           /* Descriptor size */
        CY_U3P_USB_INTRFC_DESCR,        /* Interface Descriptor type */
        0x02,                           /* Interface number */
        0x00,                           /* Alternate setting number */
        0x02,                           /* Number of end points */
        0xFF,                           /* Interface class */
        0x00,                           /* Interface sub class */
        0x00,                           /* Interface protocol code */
        0x00,                           /* Interface descriptor string index */

        /* Endpoint descriptor for producer EP */
        0x07,                           /* Descriptor size */
        CY_U3P_USB_ENDPNT_DESCR,        /* Endpoint descriptor type */
        CY_FX_EP_DEBUG_CMD,             /* Endpoint address and description */
        CY_U3P_USB_EP_BULK,             /* Bulk endpoint type */
        0x00,0x04,                      /* Max packet size = 1024 bytes */
        0x00,                           /* Servicing interval for data transfers : 0 for bulk */
    
        /* Super speed endpoint companion descriptor for producer EP */
        0x06,                           /* Descriptor size */
        CY_U3P_SS_EP_COMPN_DESCR,       /* SS endpoint companion descriptor type */
        0,                              /* No burst support. */
        0x00,                           /* Max streams for bulk EP = 0 (No streams) */
        0x00,0x00,                      /* Service interval for the EP : 0 for bulk */
    
        /* Endpoint descriptor for consumer EP */
        0x07,                           /* Descriptor size */
        CY_U3P_USB_ENDPNT_DESCR,        /* Endpoint descriptor type */
        CY_FX_EP_DEBUG_RSP,             /* Endpoint address and description */
        CY_U3P_USB_EP_BULK,             /* Bulk endpoint type */
        0x00,0x04,                      /* Max packet size = 1024 bytes */
        0x00,                           /* Servicing interval for data transfers : 0 for Bulk */
    
        /* Super speed endpoint companion descriptor for consumer EP */
        0x06,                           /* Descriptor size */
        CY_U3P_SS_EP_COMPN_DESCR,       /* SS endpoint companion descriptor type */
        0,                              /* No burst support. */
        0x00,                           /* Max streams for bulk EP = 0 (No streams) */
        0x00,0x00                       /* Service interval for the EP : 0 for bulk */
#endif
    };


/* Standard Language ID String Descriptor */
const uint8_t CyFxUSBStringLangIDDscr[] =
    {
        0x04,                           /* Descriptor Size */
        CY_U3P_USB_STRING_DESCR,        /* Device Descriptor Type */
        0x09,0x04                       /* Language ID supported */
    };

/* Standard Manufacturer String Descriptor */
const uint8_t CyFxUSBManufactureDscr[] =
    {
        0x10,                           /* Descriptor Size */
        CY_U3P_USB_STRING_DESCR,        /* Device Descriptor Type */
        'C',0x00,
        'y',0x00,
        'p',0x00,
        'r',0x00,
        'e',0x00,
        's',0x00,
        's',0x00
    };


/* Standard Product String Descriptor */
const uint8_t CyFxUSBProductDscr[] =
    {
        0x08,                           /* Descriptor Size */
        CY_U3P_USB_STRING_DESCR,        /* Device Descriptor Type */
        'F',0x00,
        'X',0x00,
        '3',0x00
    };
