circuitvalley/mipi_csi_receiver_FPGA/FPGA/tb_mipi_bridge.v

`timescale 1ns/1ns

module tb_mipi_bridge();
	reg clk;
	reg reset;
	reg mipi_clk;
	wire clk_lpp; 
	wire clk_lpn;
	wire [3:0]data_lpp;
	wire [3:0]data_lpn;
	
	reg  clk_lpp_r; 
	reg clk_lpn_r;
	reg [3:0]data_lpp_r;
	reg [3:0]data_lpn_r;
	
	reg [3:0]mipi_data;
	
	wire pclk;
	wire [31:0]data;
	wire fsync;
	wire lsync;
wire reset_g;
GSR GSR_INST (.GSR (reset_g));
PUR PUR_INST (.PUR (reset_g)); 

assign clk_lpp = clk_lpp_r;
assign clk_lpn = clk_lpn_r;
assign data_lpp = data_lpp_r;
assign data_lpn = data_lpn_r;

mipi_bridge ins1(	.clk_i(clk),
					.reset_in(reset),
					.mipi_clk_in(mipi_clk),
					.mipi_clk_lpp_io(clk_lpp),
					.mipi_clk_lpn_io(clk_lpn),
					.mipi_data_in(mipi_data),
					.mipi_data_lpp_io(data_lpp),
					.mipi_data_lpn_io(data_lpn),

					.clk_out(pclk), 
					.data_out(data),
					.fsyn_out(fsync),
					.lsync_out(lsync),
					.debug_E3(),
					.debug_F3(),
					.debug_B1(),
					.debug_D3(),
					.byte_clock_debug_H6());
					

	
initial begin										//genrate 90 phase clock and slow sync clock
	clk = 1'b0;
end
always begin
	#6 clk =  ~clk;
end

task send_mipi_frame;
	 reg [15:0]i= 16'd0;
	 begin
		 clk_lpp_r = 0;
		 clk_lpn_r = 0;
		 #5
		 send_mipi_clock();		 
		 send_mipi_clock();
		 send_mipi_clock();
		 send_mipi_clock();
		 send_mipi_clock();		 
		 send_mipi_clock();		 
		 send_mipi_clock();
		 send_mipi_clock();
		 send_mipi_clock();
		 send_mipi_clock();
		 for (i= 16'd0; i <16'd10 ; i = i +1'd1)
		 begin
		 send_line();
		 #20;
		 end
		 send_mipi_clock();
		 send_mipi_clock();
		 send_mipi_clock();
		 send_mipi_clock();
		 send_mipi_clock();
		 send_mipi_clock();
		 send_mipi_clock();
		 send_mipi_clock();
		 send_mipi_clock();
		 #5
		 clk_lpp_r = 1;
		 clk_lpn_r = 1;

	 end
endtask

task send_line;
	reg[15:0]i = 16'b0;
	begin
	

		send_mipi_clock();
		send_mipi_clock();
		send_mipi_clock();
		data_lpp_r = 4'b0;
		send_mipi_clock();
		send_mipi_clock();
		send_mipi_clock();
		data_lpn_r = 4'b0;
		send_mipi_byte(32'hB8B8B8B8);
		send_mipi_byte(32'h2B600900);
		for (i= 16'b0; i < 16'd120 ; i = i+1)
		begin
			send_mipi_byte(32'h00FF55AA);
			send_mipi_byte(32'h0000FF55);
			send_mipi_byte(32'hAA0000FF);
			send_mipi_byte(32'h55AA0000);
			send_mipi_byte(32'hFF55AA00);
		end
		send_mipi_clock();
		send_mipi_clock();		
		data_lpp_r = 4'b1111;
		data_lpn_r = 4'b1111;
		
	end
endtask

task send_mipi_byte;
	input [31:0]bytes;
	reg [7:0] i = 8'b0;
	begin
		for(i = 8'b0; i< 8'h8; i = i+2) begin
			#1;
			mipi_data = {bytes[i], bytes[8'd8 + i] ,bytes[8'd16 +i] , bytes[8'd24 + i]};
			#1;
			mipi_clk = 1'b1;
			#1;
			mipi_data = {bytes[i+1], bytes[8'd8 +i + 1] ,bytes[8'd16 + i +1] , bytes[8'd24 + i + 1]};
			#1;
			mipi_clk = 1'b0;
		end 
	end	
endtask

task send_mipi_clock;
	begin
		send_mipi_byte(32'h00000000);
	end
endtask

initial begin
	mipi_data = 0;
	mipi_clk = 0;
	data_lpp_r = 4'b1111;
	data_lpn_r = 4'b1111;
	 reset = 0;
	clk_lpp_r = 1;
	clk_lpn_r = 1;
	#20
	reset = 1; 
	#200
	send_mipi_frame();
	#200
	send_mipi_frame();

	#200
	send_mipi_frame();
end

endmodule
