circuitvalley/mipi_csi_receiver_FPGA/FPGA/mipi_csi_packet_decoder.v

`timescale 1ns/1ns

/*
MIPI CSI RX to Parallel Bridge (c) by Gaurav Singh www.CircuitValley.com

MIPI CSI RX to Parallel Bridge is licensed under a
Creative Commons Attribution 3.0 Unported License.

You should have received a copy of the license along with this
work.  If not, see <http://creativecommons.org/licenses/by/3.0/>.
*/

/*
Basically a packet Stripper, removes header and footer from packet 
Takes lane aligned data from lane aligner @ mipi byte clock
looks for specific packet type, in this case RAW10bit 0x2B
outputs Stripped bytes in exactly the way they were received.
this module also fetch packet length and output_valid is active as long as input data is valid and packet length is still valid.
*/

module mipi_csi_packet_decoder(
								clk_i,
								data_valid_i,
								data_i,
								output_valid_o,
								data_o,
								packet_length
								);
								
localparam [7:0]SYNC_BYTE = 8'hB8;
localparam [3:0]LANES = 3'h4;
localparam [7:0]MIPI_CSI_PACKET_10bRAW = 8'h2B;
input clk_i;
input data_valid_i;
input [31:0]data_i;
output reg output_valid_o;
output reg [31:0]data_o;
output reg [31:0]packet_length;
reg [31:0]packet_length_reg;

reg [31:0]last_data_i;

always @(negedge clk_i)
begin
	if (data_valid_i)
	begin
		last_data_i <= data_i;
		output_valid_o <= |packet_length_reg;
		data_o <= data_i;
		
		if (|packet_length_reg)
		begin
			packet_length_reg <= packet_length_reg - LANES;
		end
		else if (last_data_i[7:0] == SYNC_BYTE && data_i[7:0] == MIPI_CSI_PACKET_10bRAW)
		begin
			packet_length_reg <= {data_i[23:16], data_i[15:8]};
			packet_length <= {data_i[23:16], data_i[15:8]};
		end
	end
	else 
	begin
		last_data_i <=32'h0;
		data_o <=32'h0;
		packet_length <= 32'h0;
		packet_length_reg <= 32'h0;
		output_valid_o <= 1'h0;
	end
end

endmodule
